jbilander/sdbox/images/_renders/vFinal-back.png

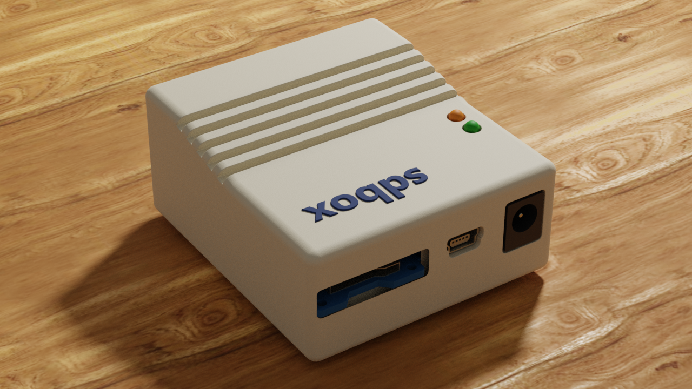
images/_renders/vFinal-back.png
