jbilander/sdbox/images/_renders/vFinal-front-dof.png

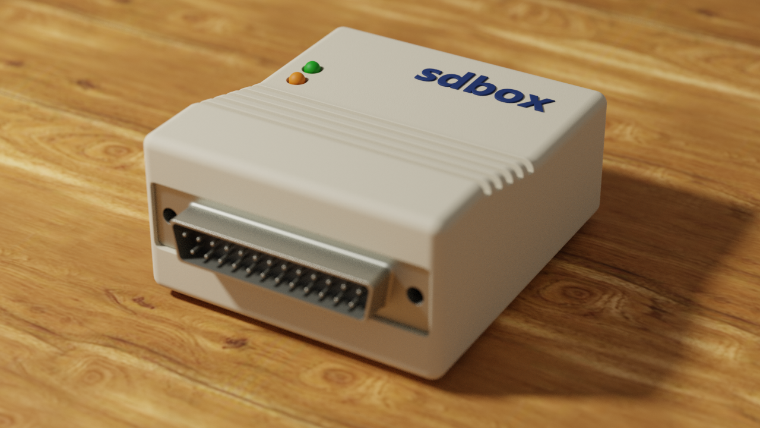
images/_renders/vFinal-front-dof.png
