jbilander/sdbox/images/_renders/vFinal-open-back.png

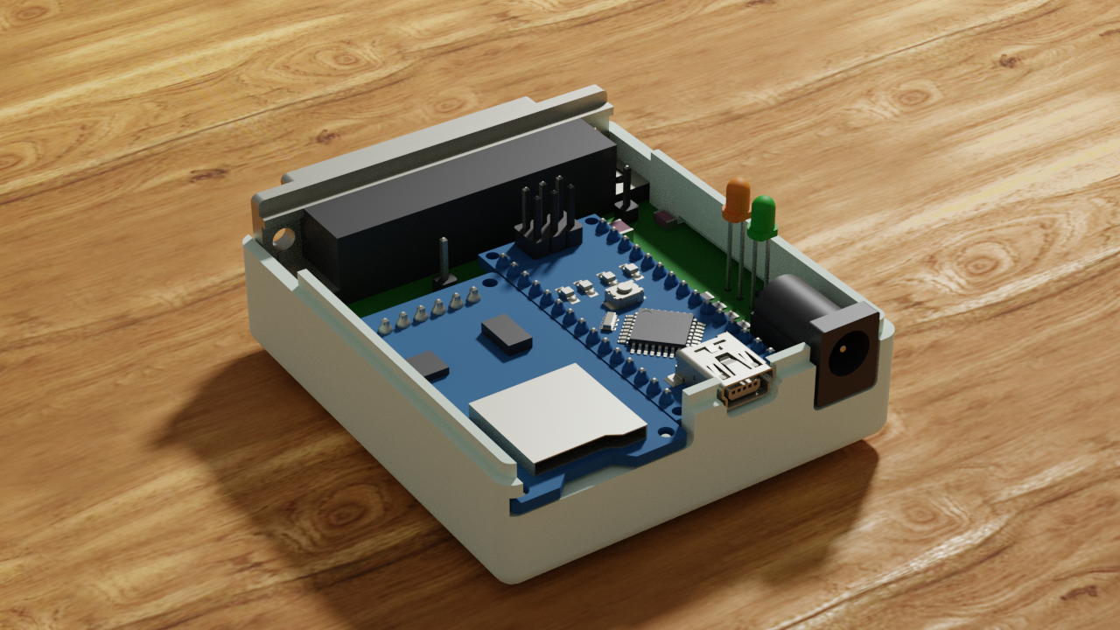
images/_renders/vFinal-open-back.png
