jbilander/sdbox/images/_renders/vFinal-open-front.png

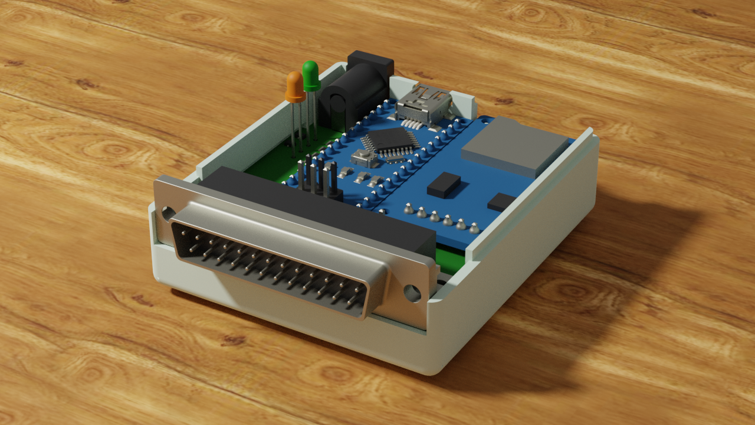
images/_renders/vFinal-open-front.png
